pedaleECP/pedalSensors/Documentation/Diagrames&Pictures/DescriptionCapteurs.png

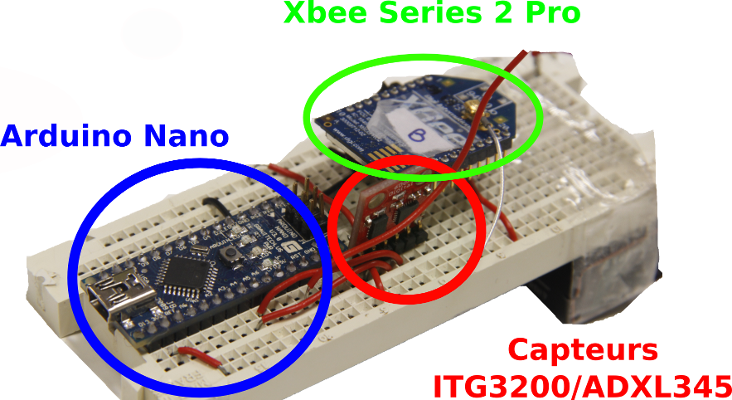
Documentation/Diagrames&Pictures/DescriptionCapteurs.png
