pedaleECP/pedalSensors/Documentation/Diagrames&Pictures/DescriptionPedale.png

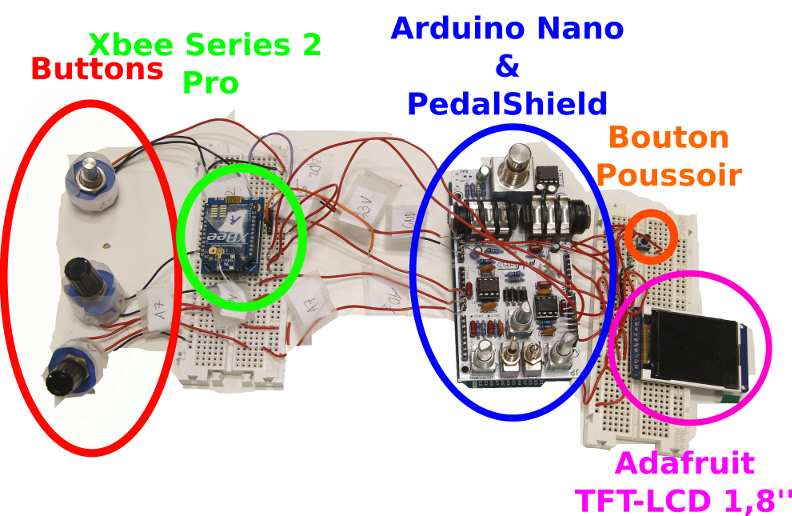
Documentation/Diagrames&Pictures/DescriptionPedale.png
