pedaleECP/pedalSensors/Documentation/Photos/2014-10-13 Integration des Nouvelles Potentiomètres/IMG-20141013-WA0008.jpg

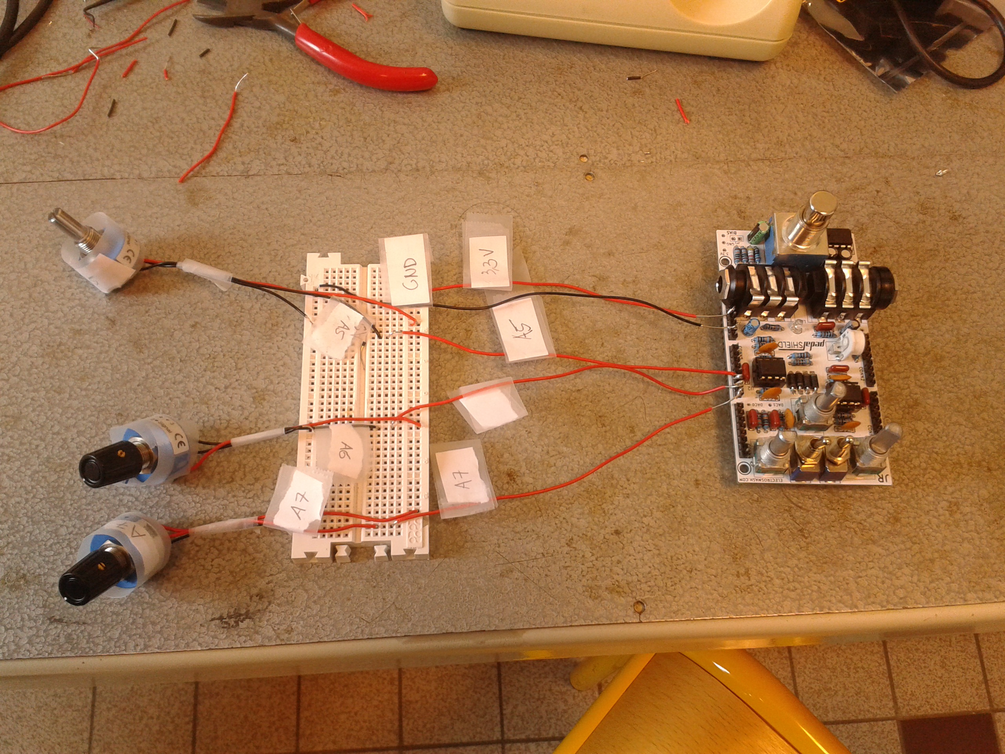
Documentation/Photos/2014-10-13 Integration des Nouvelles Potentiomètres/IMG-20141013-WA0008.jpg
