pedaleECP/pedalSensors/Documentation/Photos/2014-10-13 Integration des Nouvelles Potentiomètres/IMG_20141013_122142.jpg

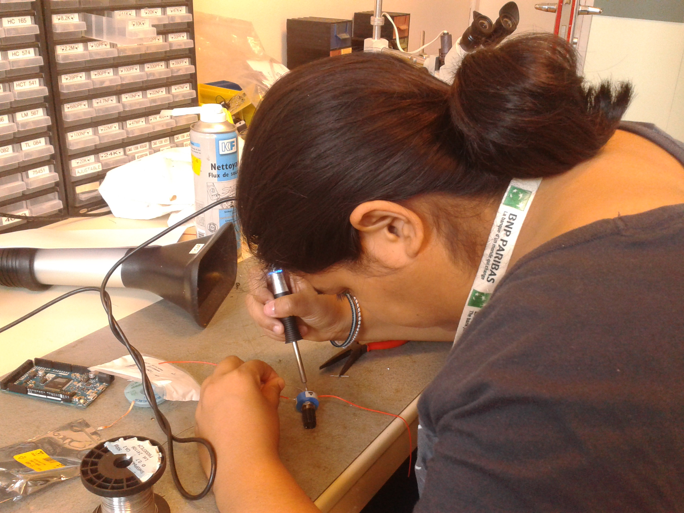
Documentation/Photos/2014-10-13 Integration des Nouvelles Potentiomètres/IMG_20141013_122142.jpg
