pedaleECP/pedalSensors/Documentation/Photos/2014-11-04 Scéance 5: Conection du capteur et codage/IMG_20141104_153709.jpg

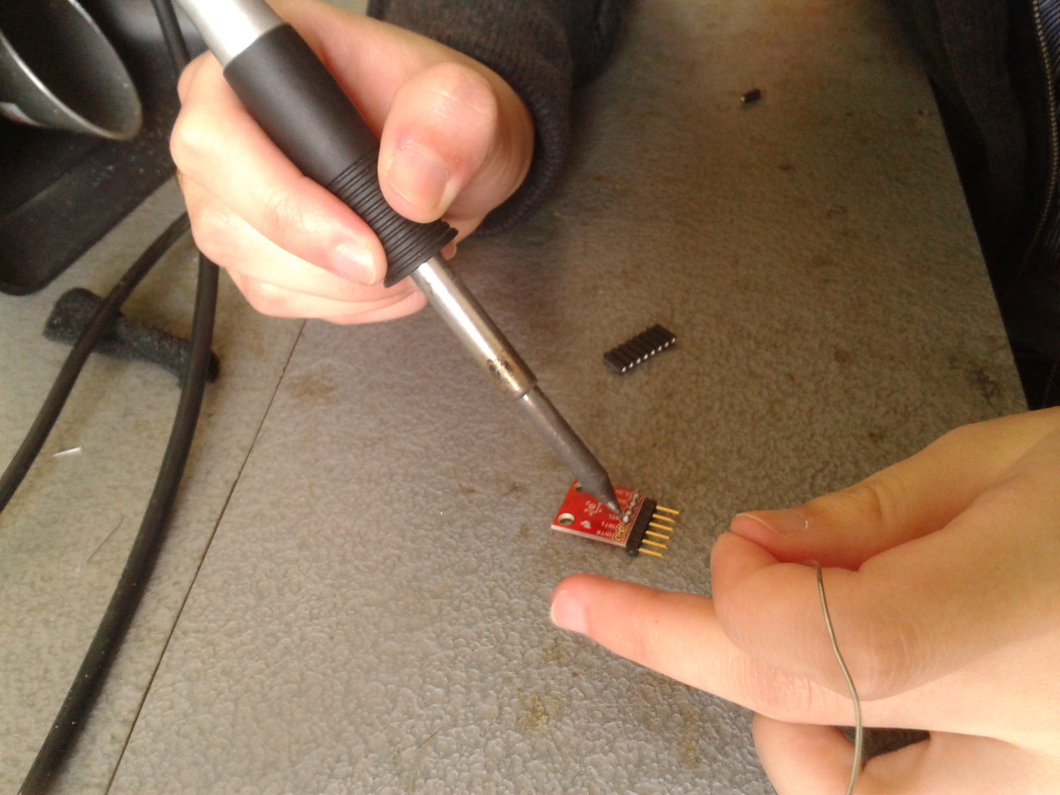
Documentation/Photos/2014-11-04 Scéance 5: Conection du capteur et codage/IMG_20141104_153709.jpg
