pedaleECP/pedalSensors/Documentation/Photos/2014-11-17 Séance 7/IMG-20141125-WA0008.jpg

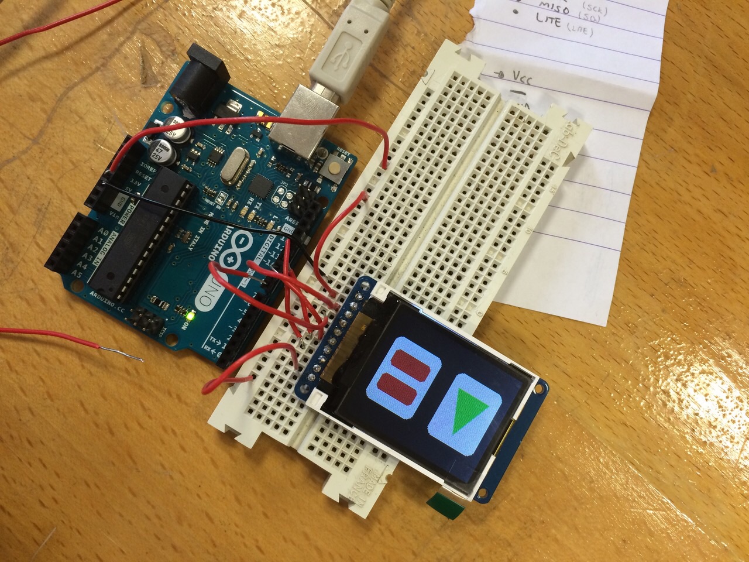
Documentation/Photos/2014-11-17 Séance 7/IMG-20141125-WA0008.jpg
