pedaleECP/pedalSensors/Documentation/Photos/2014-11-17 Séance 7/IMG_20141117_105002.jpg

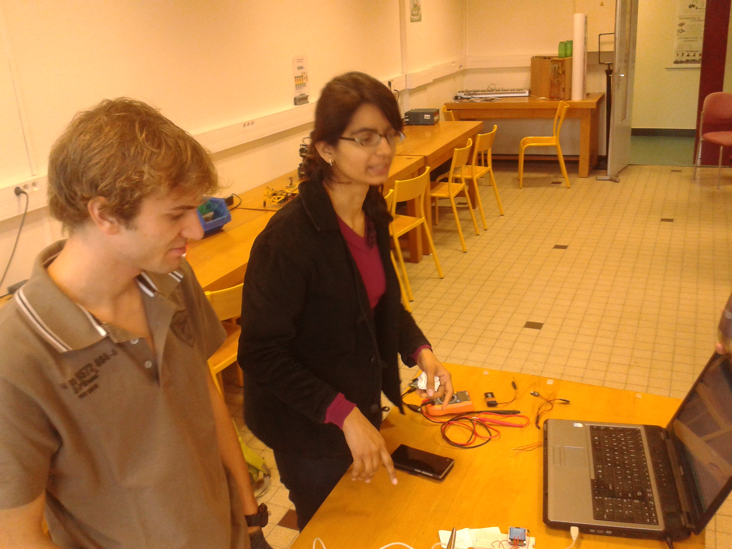
Documentation/Photos/2014-11-17 Séance 7/IMG_20141117_105002.jpg
