pedaleECP/pedalSensors/Documentation/Photos/2014-11-25 Séance 8 - Tout marche!/IMG_20141125_103552.jpg

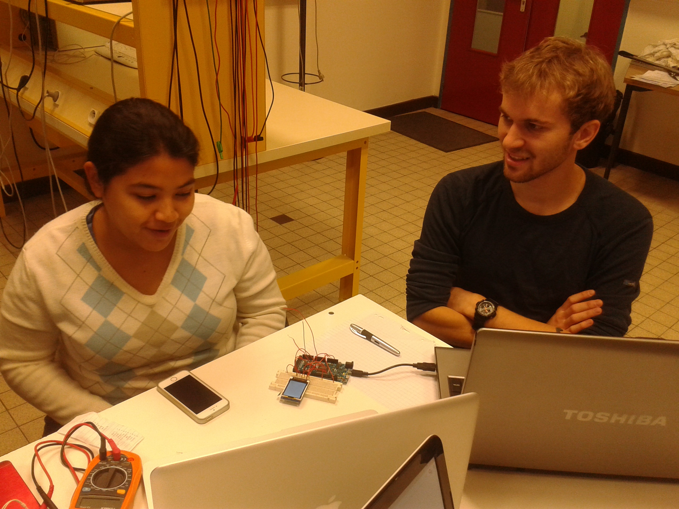
Documentation/Photos/2014-11-25 Séance 8 - Tout marche!/IMG_20141125_103552.jpg
