pedaleECP/pedalSensors/Documentation/Photos/2014-11-25 Séance 8 - Tout marche!/Putting our adapted library online.png

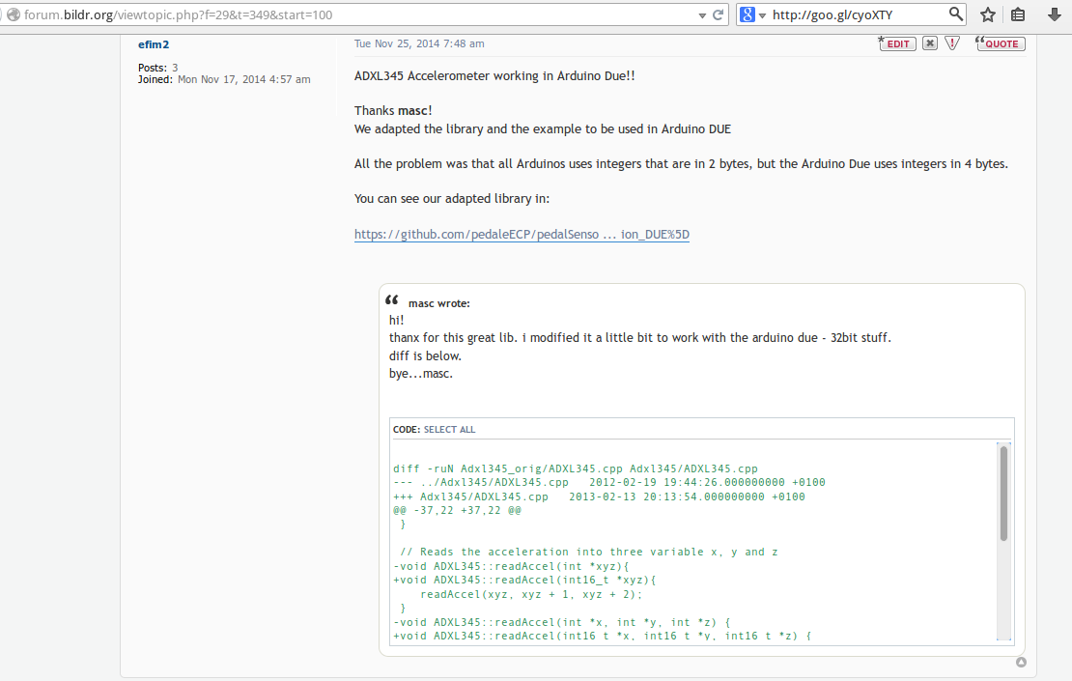
Documentation/Photos/2014-11-25 Séance 8 - Tout marche!/Putting our adapted library online.png
