pedaleECP/pedalSensors/Documentation/Photos/AsanaScreenshot.png

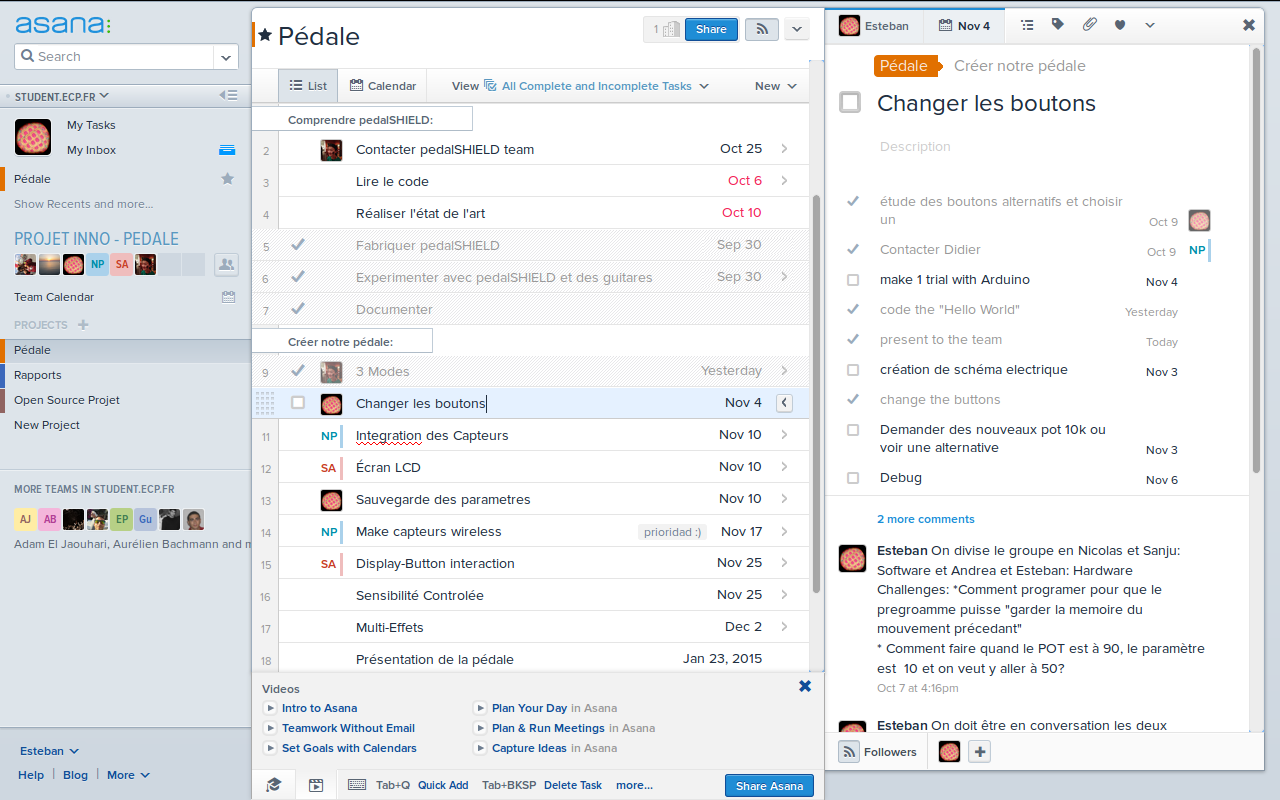
Documentation/Photos/AsanaScreenshot.png
