pedaleECP/pedalSensors/Documentation/Photos/GitHubScrooshot.png

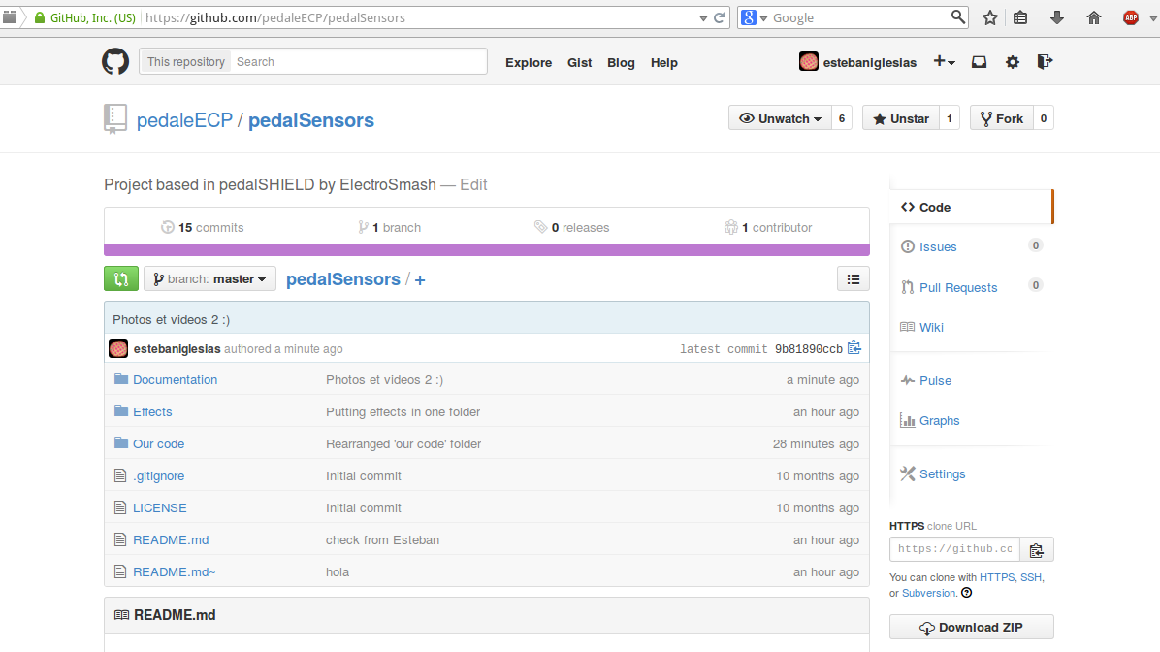
Documentation/Photos/GitHubScrooshot.png
