pedaleECP/pedalSensors/Documentation/Sensor/6dof(Arduino)[V7]/6DOF_arduino_hookup.png.png

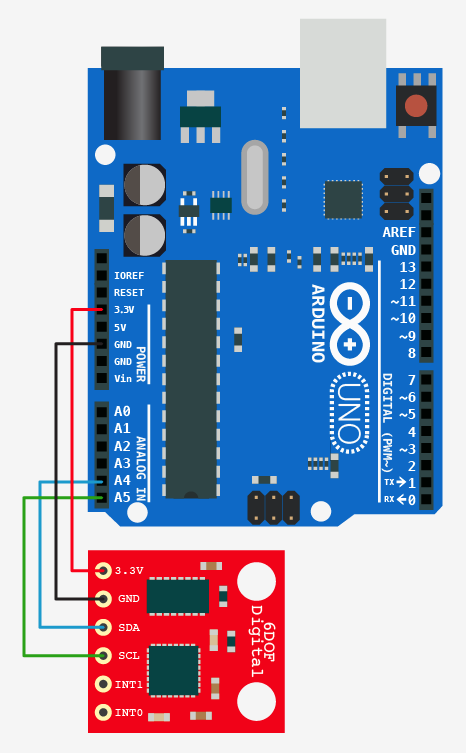
Documentation/Sensor/6dof(Arduino)[V7]/6DOF_arduino_hookup.png.png
