pedaleECP/pedalSensors/Documentation/Photos/2014-09-30 Scéance 2 - Fabrication du pedalSHIELD/IMG_3901.JPG

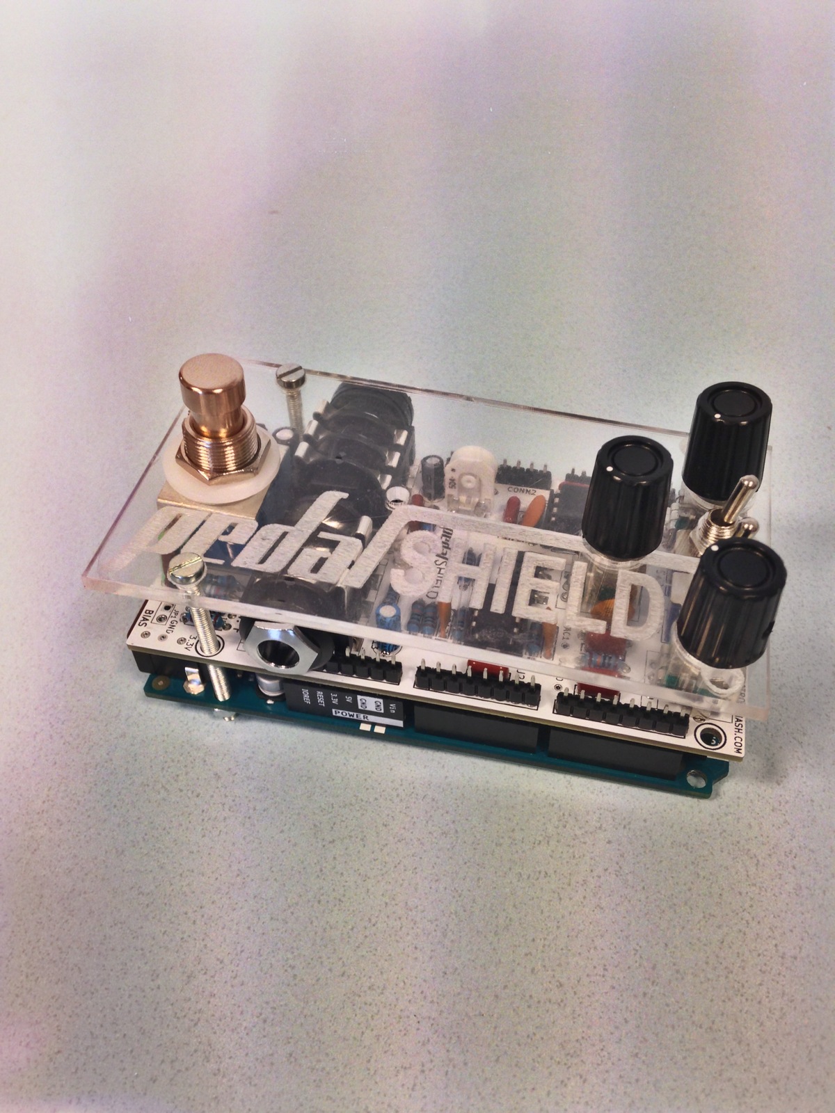
Documentation/Photos/2014-09-30 Scéance 2 - Fabrication du pedalSHIELD/IMG_3901.JPG
