pedaleECP/pedalSensors/Documentation/Photos/2014-09-30 Scéance 2 - Fabrication du pedalSHIELD/IMG_20140930_173709.jpg

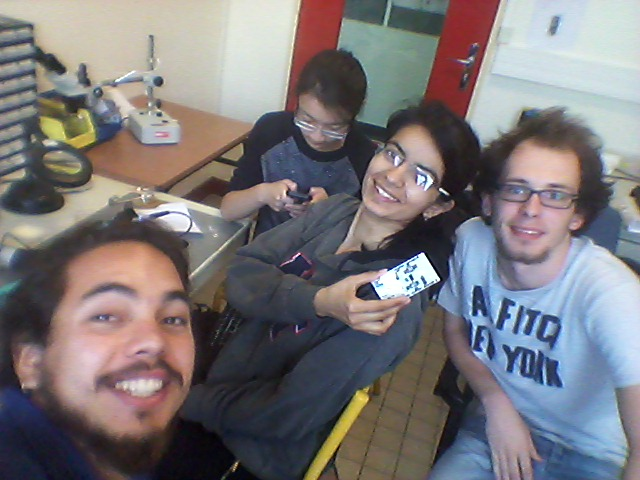
Documentation/Photos/2014-09-30 Scéance 2 - Fabrication du pedalSHIELD/IMG_20140930_173709.jpg
