pedaleECP/pedalSensors/Documentation/Photos/2014-11-11 Séance 6 - Experimentation des capteurs/IMG_20141111_121510.jpg

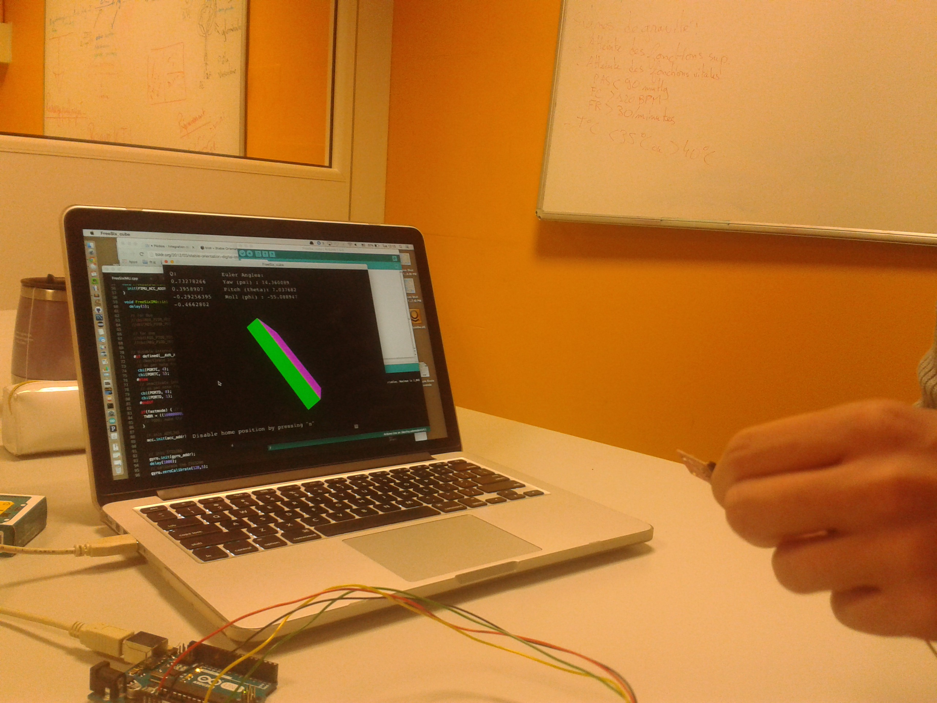
Documentation/Photos/2014-11-11 Séance 6 - Experimentation des capteurs/IMG_20141111_121510.jpg
