pedaleECP/pedalSensors/Documentation/Photos/2014-11-11 Séance 6 - Experimentation des capteurs/IMG_20141111_121516.jpg

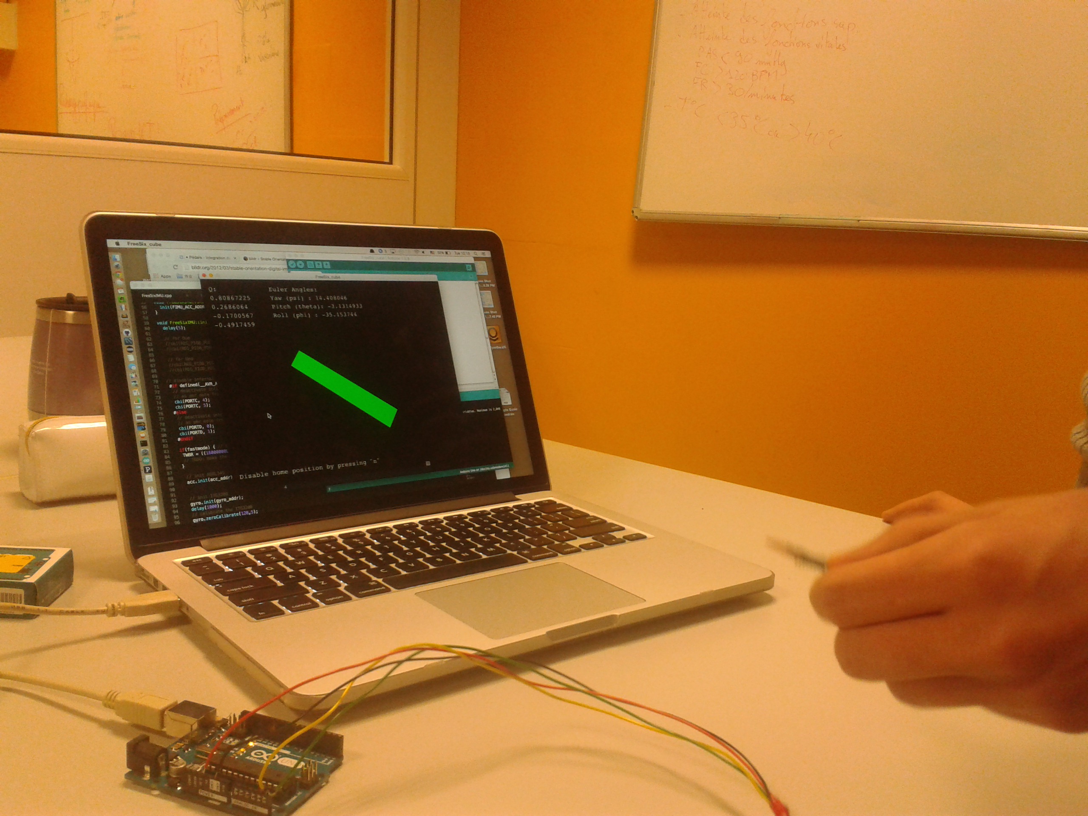
Documentation/Photos/2014-11-11 Séance 6 - Experimentation des capteurs/IMG_20141111_121516.jpg
