pedaleECP/pedalSensors/Our code/continuousButtonsFinal1/continuousButtonsFinal1.ino

// Licensed under a Creative Commons Attribution 3.0 Unported License.
// Based on rcarduino.blogspot.com previous work.
// www.electrosmash.com/pedalshield

// Code pour tester les neauveaux potentiometres
 
int in_ADC0, in_ADC1;  //variables for 2 ADCs values (ADC0, ADC1)
int POT0, POT1, POT2, out_DAC0, out_DAC1; //variables for 3 pots (ADC8, ADC9, ADC10)
int LED = 3;
int FOOTSWITCH = 7; 
int TOGGLE = 2; 

int MAXPOT = 4096;

// Ici on teste avec un seul pot.

int MEMORYPOTMOD = 0; // Valeur precedent de POTMOD
int POTMOD = 0; //Valeur de la sortie
int VALUE = 0; //Valeur à rajouter au paramètre
int Pot2Max = 10000;
int Pot2Min = 0;

int Pot2Limit = 10000;

void setup()
{
  //ADC Configuration
  ADC->ADC_MR |= 0x80;   // DAC in free running mode.
  ADC->ADC_CR=2;         // Starts ADC conversion.
  ADC->ADC_CHER=0xFFFF;  // Enable all ADC channels   
 ADC->ADC_CHER = 0xFFFF;
// ADC->ADC_CHER=0x1CC0;  // Enable ADC channels 0 and 1. 
  
  
 
  //DAC Configuration
  analogWrite(DAC0,0);  // Enables DAC0
  analogWrite(DAC1,0);  // Enables DAC0
  Serial.begin(57600);

}
 
void loop()
{
  //Read the ADCs
  while((ADC->ADC_ISR & 0x1CC0)!=0x1CC0);// wait for ADC 0, 1, 8, 9, 10 conversion complete.
  in_ADC0=ADC->ADC_CDR[7];               // read data from ADC0
  in_ADC1=ADC->ADC_CDR[6];               // read data from ADC1
  
  POT0=ADC->ADC_CDR[10];                 // read data from ADC10
  POT1=ADC->ADC_CDR[11];                 // read data from ADC11  
  POTMOD=ADC->ADC_CDR[0];                 // read data from ADC12 POTMOD c'est pour la lecture, POT2 va controler le son.
  

  //we divide in 4 cases : 
  //the first when the button is turned clockwise (direction of increasing value) and it crosses zero
  //the second when the button is turned anti clockwise (direction of decreasing value) and it crosses zero
  //the third when the button is turned clockwise (direction of increasing value) and it doesn't cross zero
  //the fourth when the button is turned anti clockwise (direction of decreasing value) and it doesn't cross zero
  
  //the variable POT2 is the previous value of the output
  //the variable VALUE signifies the absolute change in the reading of potentiometer while making the turn
  //by comparing the POT2+VALUE with the range of output, we decide the final value of the output
  
  
  if ((POTMOD - MEMORYPOTMOD) < -0.9*MAXPOT) {
    VALUE = MAXPOT + POTMOD - MEMORYPOTMOD;//+POTSENSOR 
    
    if((POT2 +VALUE) > Pot2Max) {
       POT2 = Pot2Max;
   }
    else { 
       POT2 = POT2 + VALUE ;
   }
   }
  
  
  else if ((POTMOD - MEMORYPOTMOD) > 0.9*MAXPOT) {
    VALUE = - (MAXPOT) + POTMOD - MEMORYPOTMOD;//+POTSENSOR
    if((POT2 +VALUE) < Pot2Min) {
       POT2 = Pot2Min;
   }
    else { 
       POT2 = POT2 + VALUE ;
   }
  }
  
     
  else if ((POTMOD - MEMORYPOTMOD) > 0) {
   VALUE = POTMOD - MEMORYPOTMOD;//+POTSENSOR
    if((POT2 +VALUE) > Pot2Max) {
       POT2 = Pot2Max;
    }
     else { 
       POT2 = POT2 + VALUE ;
    }
   }
  
     
  else if ((POTMOD - MEMORYPOTMOD) <0) {
    VALUE = POTMOD - MEMORYPOTMOD;//+POTSENSOR
    if((POT2 + VALUE) < Pot2Min) {
       POT2 = Pot2Min;
    }
     else { 
       POT2 = POT2 + VALUE ;
    }
   }
   MEMORYPOTMOD=POTMOD ;


  //Serial.println("POTMOD: ");
  //Serial.print("\t");    // prints a tab
  //Serial.print(POTMOD);
  //Serial.print("\t");    // prints a tab  
  //Serial.println("POT2:    ... ");
  //Serial.print(POT2);
  //Serial.println("");      // prints another carriage return
  //Serial.println("MEMORY POTMOD: ");
  //Serial.print("\t");    // prints a tab
  //Serial.print(MEMORYPOTMOD);
  
  //delay(200);

   //TODO : Add a second pot with the sensors
     
  //Add volume feature with POT2
  out_DAC0=map(in_ADC0,0,4095,1,POT2);
  out_DAC1=map(in_ADC1,0,4095,1,POT2);
   
  //Write the DACs
  dacc_set_channel_selection(DACC_INTERFACE, 0);       //select DAC channel 0
  dacc_write_conversion_data(DACC_INTERFACE, out_DAC0);//write on DAC
  dacc_set_channel_selection(DACC_INTERFACE, 1);       //select DAC channel 1
  dacc_write_conversion_data(DACC_INTERFACE, out_DAC1);//write on DAC
}
